sudo-apt-install-tap/Tap65/images/Closeup shot of neopixels.jpeg

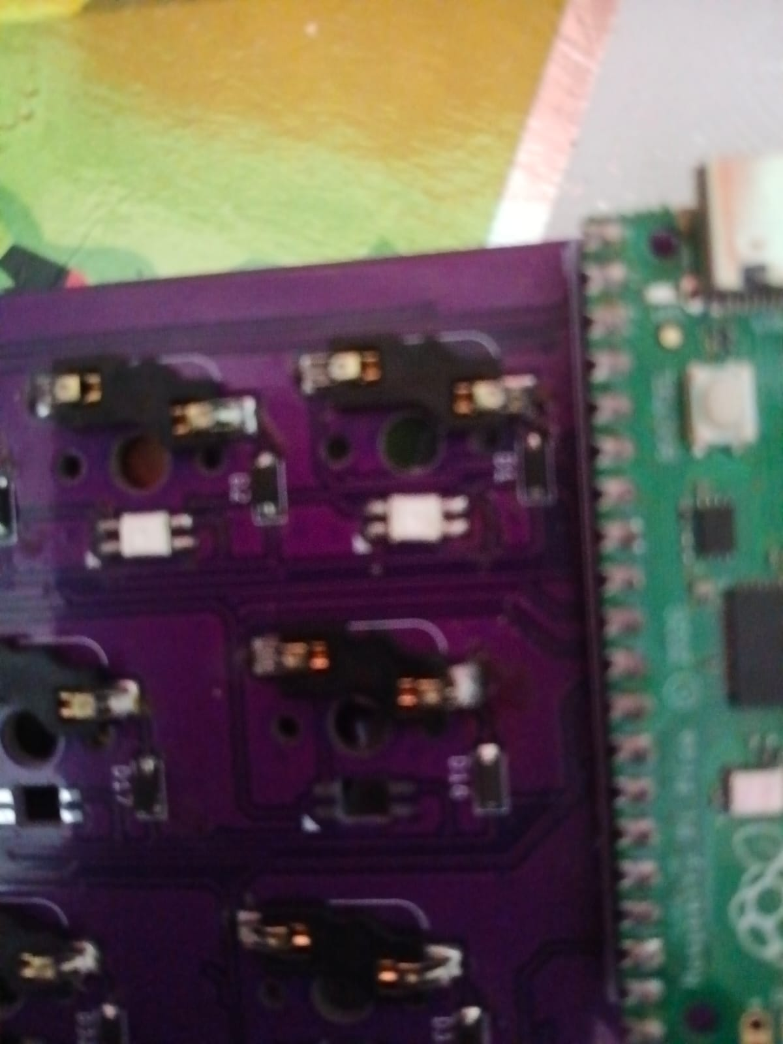
images/Closeup shot of neopixels.jpeg
