sudo-apt-install-tap/Tap65/images/cool shot.jpeg

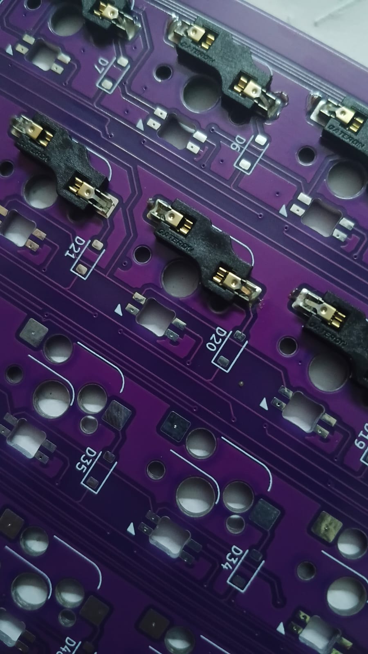
images/cool shot.jpeg
