sudo-apt-install-tap/Tap65/images/Finished PCB.jpeg

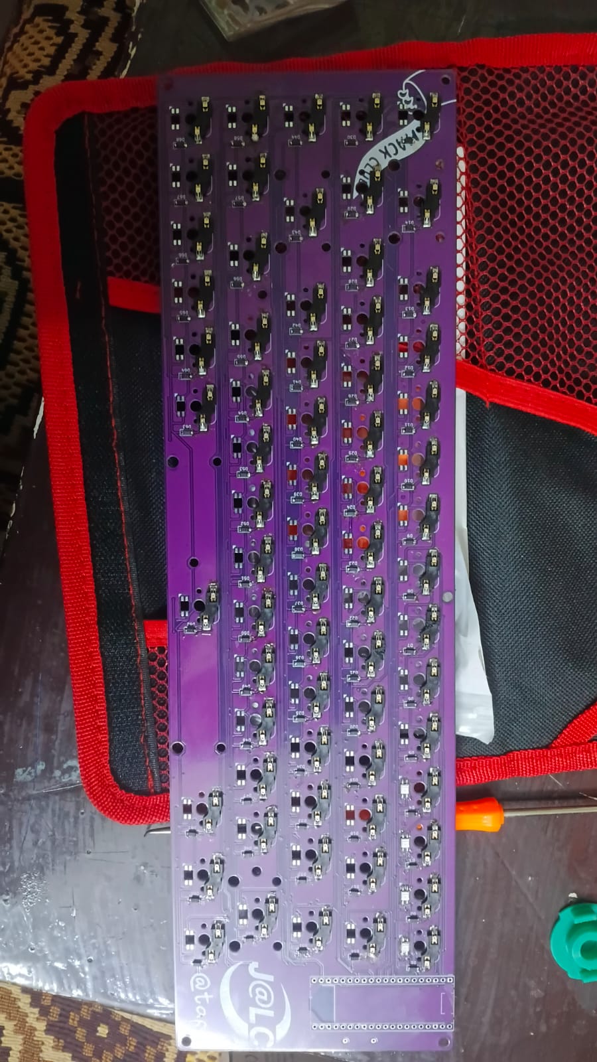
images/Finished PCB.jpeg
