sudo-apt-install-tap/Tap65/images/Finished(withStabs).jpeg

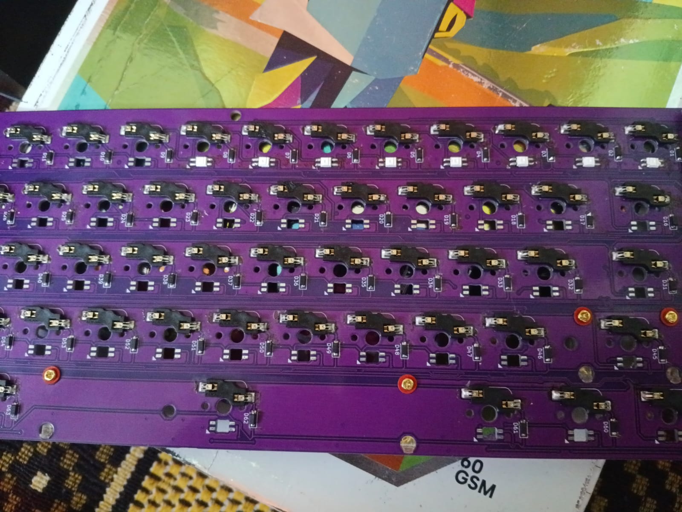
images/Finished(withStabs).jpeg
