sudo-apt-install-tap/Tap65/images/grips.jpeg

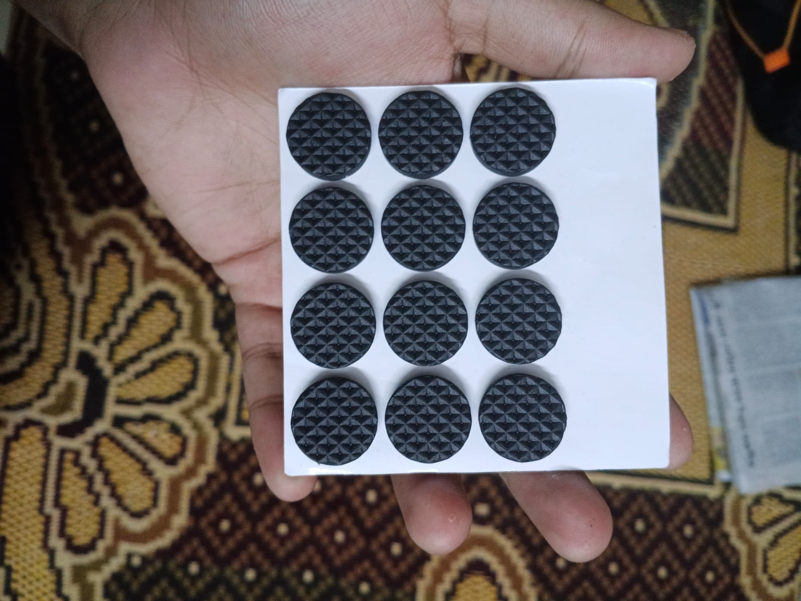
images/grips.jpeg
