sudo-apt-install-tap/Tap65/images/Half Finished PCB 2.jpeg

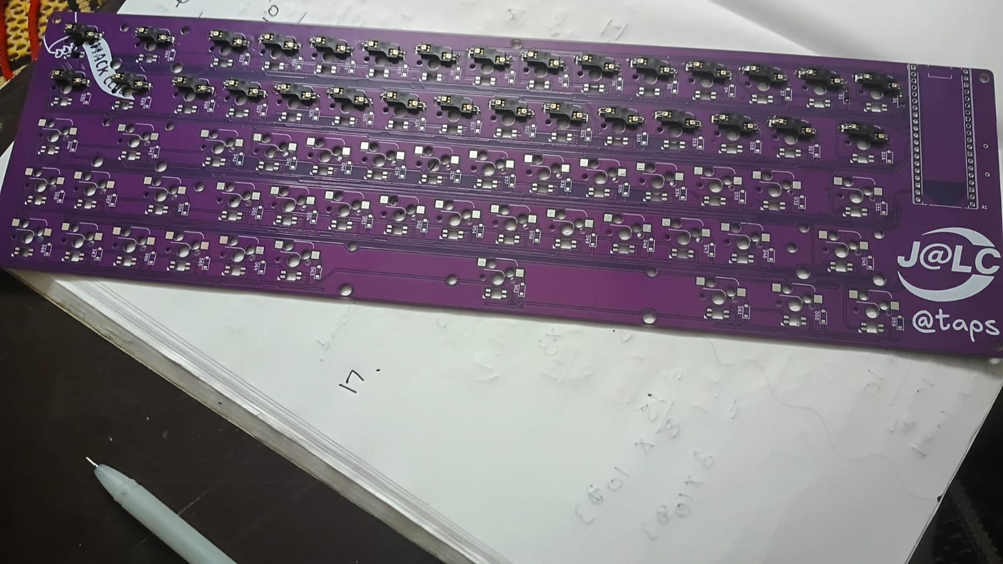
images/Half Finished PCB 2.jpeg
