sudo-apt-install-tap/Tap65/images/Initial Neopixles.jpeg

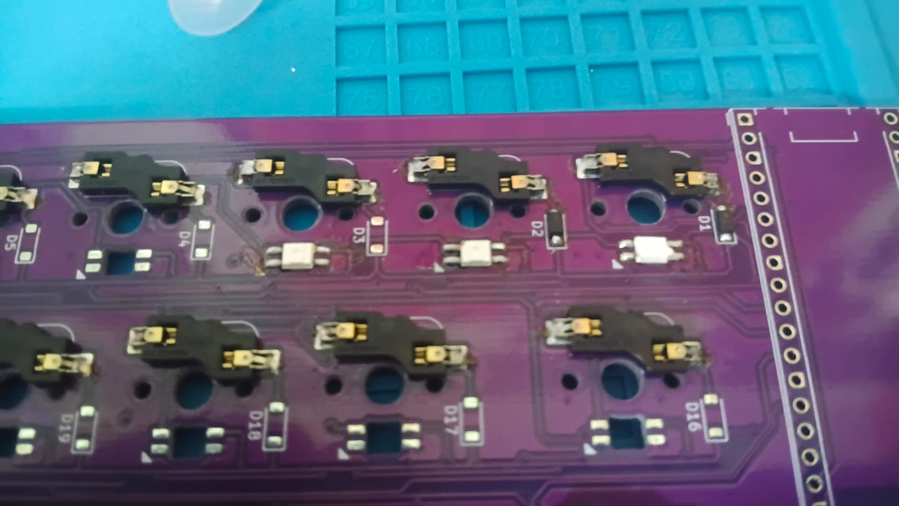
images/Initial Neopixles.jpeg
