sudo-apt-install-tap/Tap65/images/Keycaps.jpeg

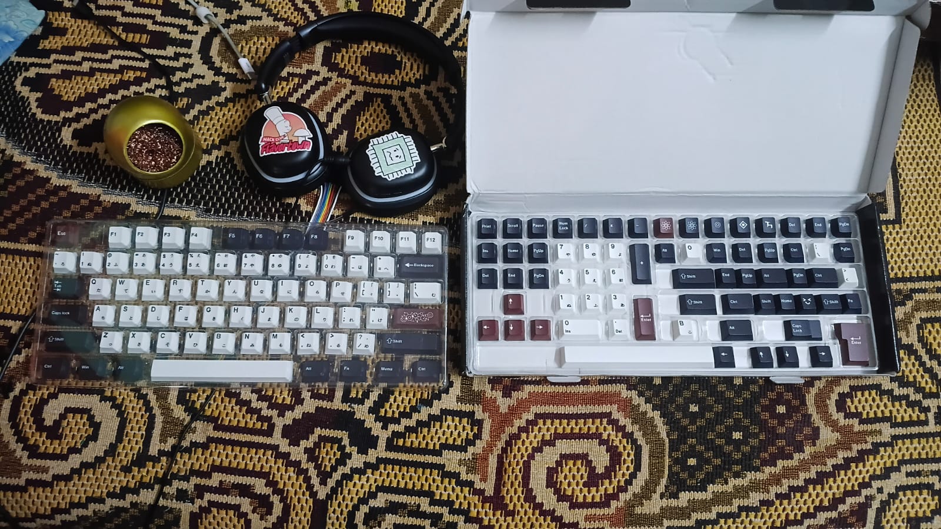
images/Keycaps.jpeg
