sudo-apt-install-tap/Tap65/images/PCB Stabalizer Fit.jpeg

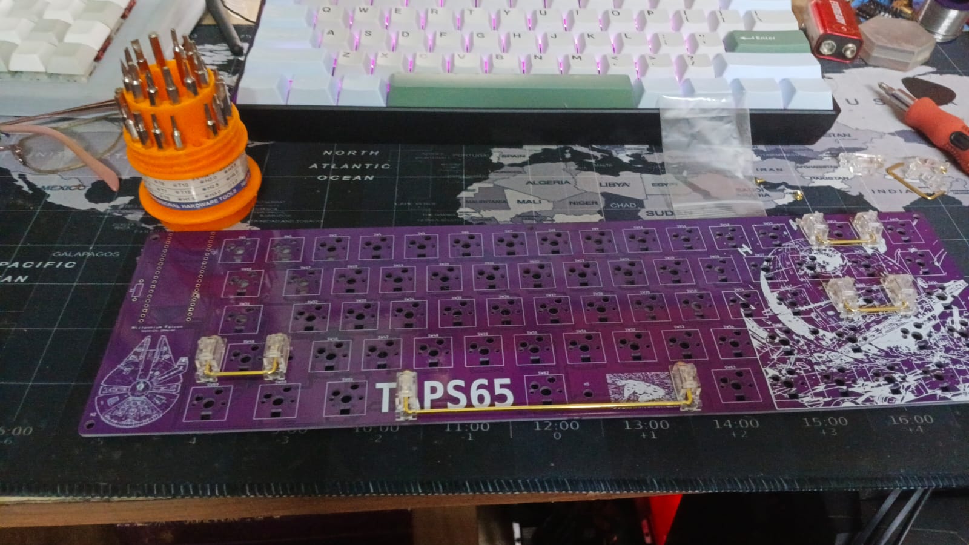
images/PCB Stabalizer Fit.jpeg
