sudo-apt-install-tap/Tap65/images/PCB.jpeg

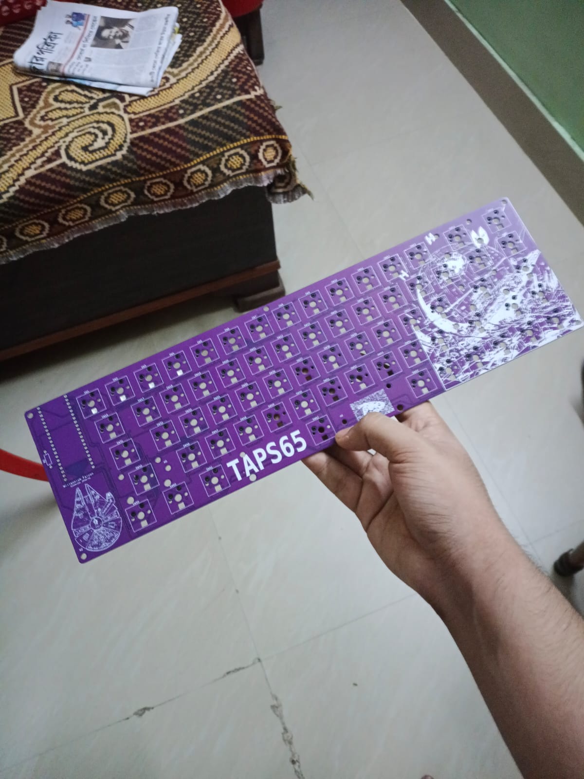
images/PCB.jpeg
