sudo-apt-install-tap/Tap65/images/PCBs DAY1.jpeg

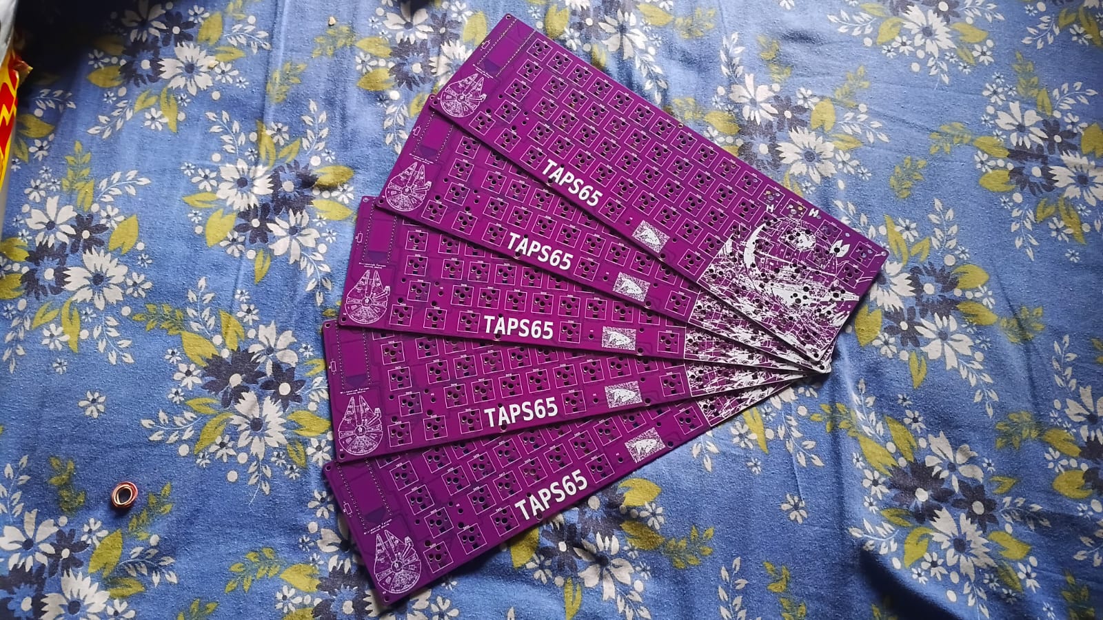
images/PCBs DAY1.jpeg
