sudo-apt-install-tap/Tap65/images/clone soldered on.jpeg

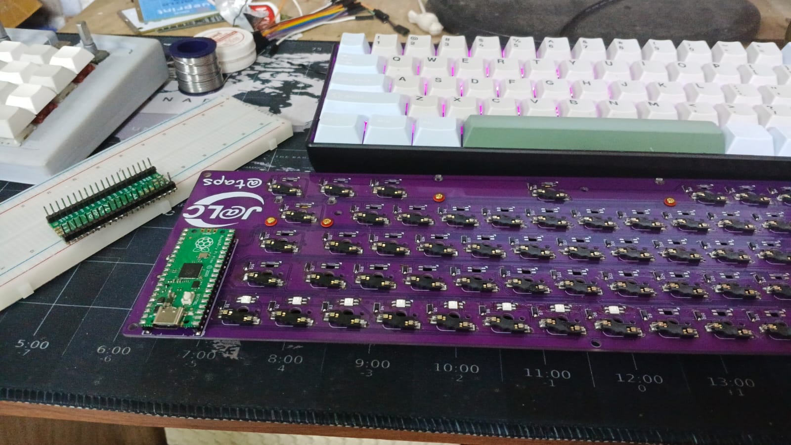
images/clone soldered on.jpeg
