sudo-apt-install-tap/Tap65/images/Soldering.jpeg

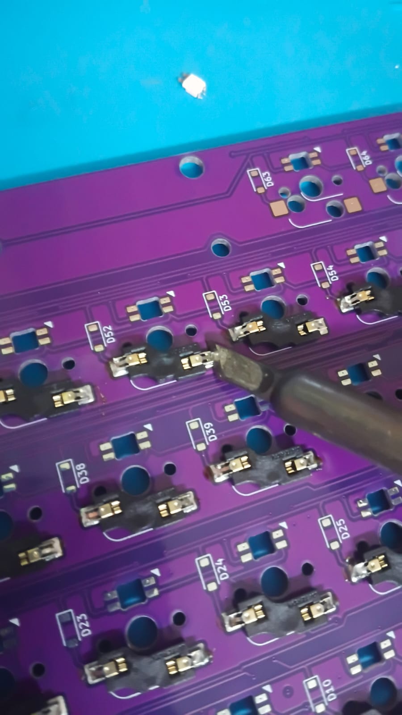
images/Soldering.jpeg
